danbowles/klorball35/output/outlines/combo_left.dxf

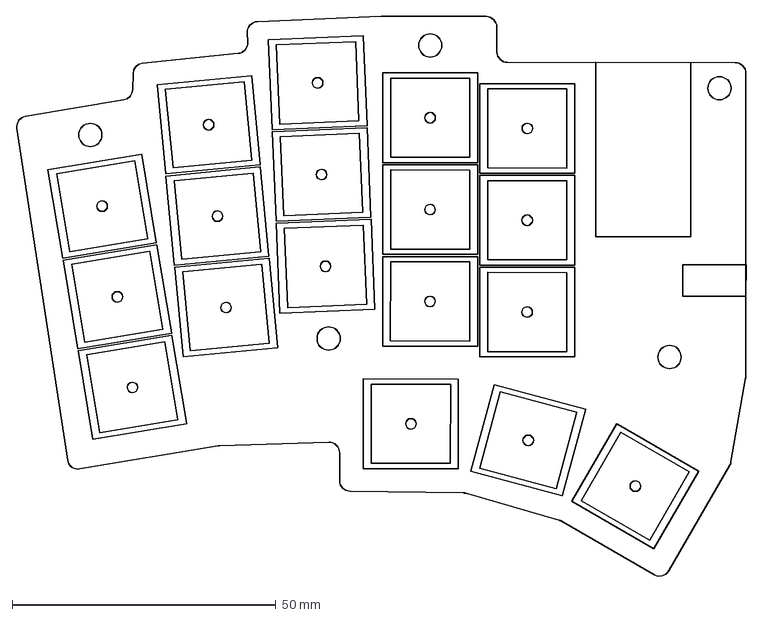
[picture p19: CAD file, 2026-06-25]
output/outlines/combo_left.dxf
138.3 x 106.4 mm
