danbowles/klorball35/output/outlines/trackball_breakout_right.dxf

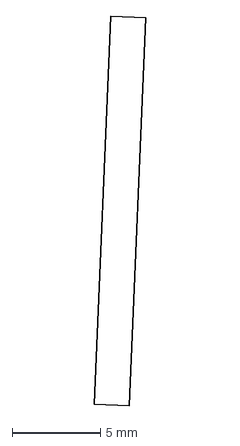
[picture p20: CAD file, 2026-06-25]
output/outlines/trackball_breakout_right.dxf
2.94 x 22.1 mm
