danbowles/klorball35/output/outlines/keycaps_left.dxf

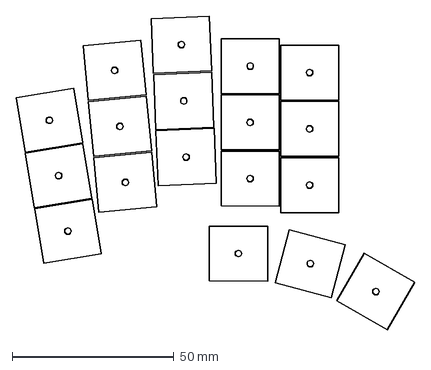
[picture p21: CAD file, 2026-06-25]
output/outlines/keycaps_left.dxf
123.3 x 97.2 mm
