danbowles/klorball35/output/outlines/trrs_left.dxf

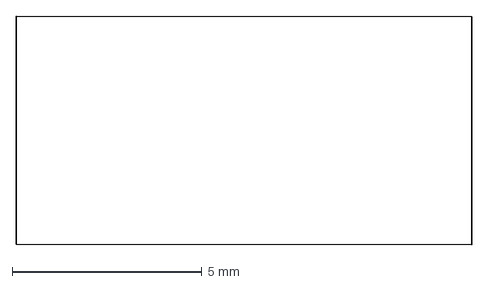
[picture p22: CAD file, 2026-06-25]
output/outlines/trrs_left.dxf
12.0 x 6.01 mm
